gianluca-rainis/Z80DevBoard/images/Z80DevBoard.png

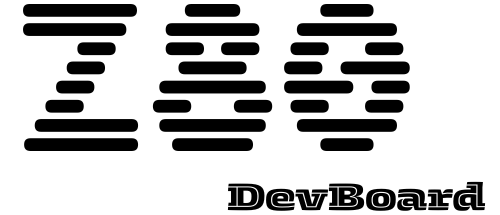
images/Z80DevBoard.png
